beau-seidon/Promicroboy/other resources/build photos/back.jpg

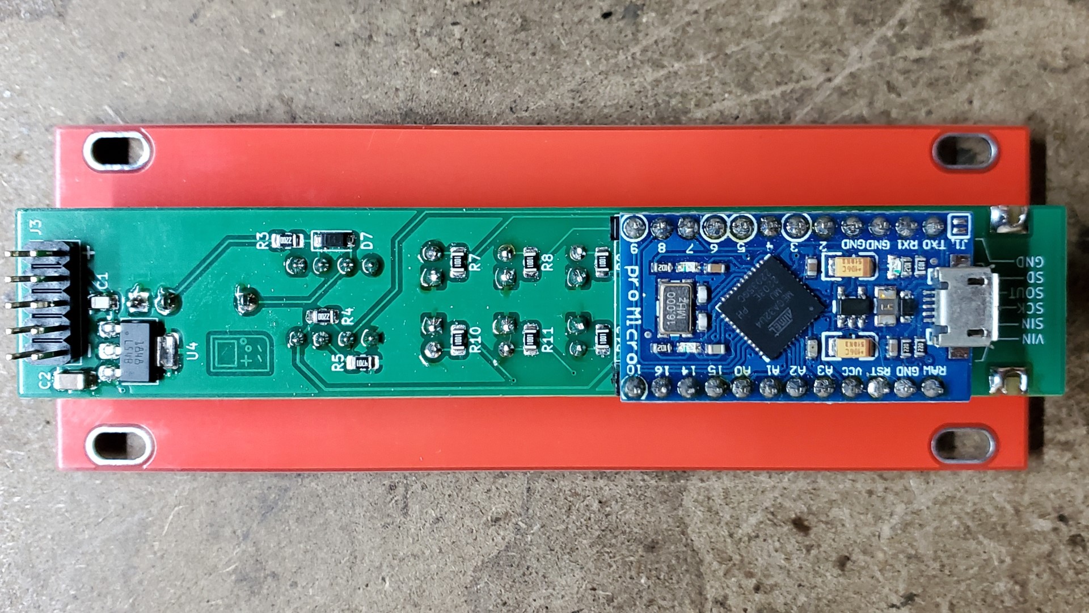
other resources/build photos/back.jpg
