beau-seidon/Promicroboy/other resources/build photos/link2.jpg

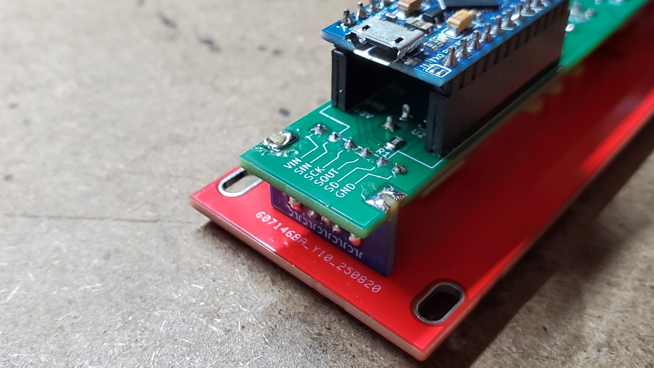
other resources/build photos/link2.jpg
