beau-seidon/Promicroboy/hardware/ProMicro16MHzv2.pdf

## Name

## Power

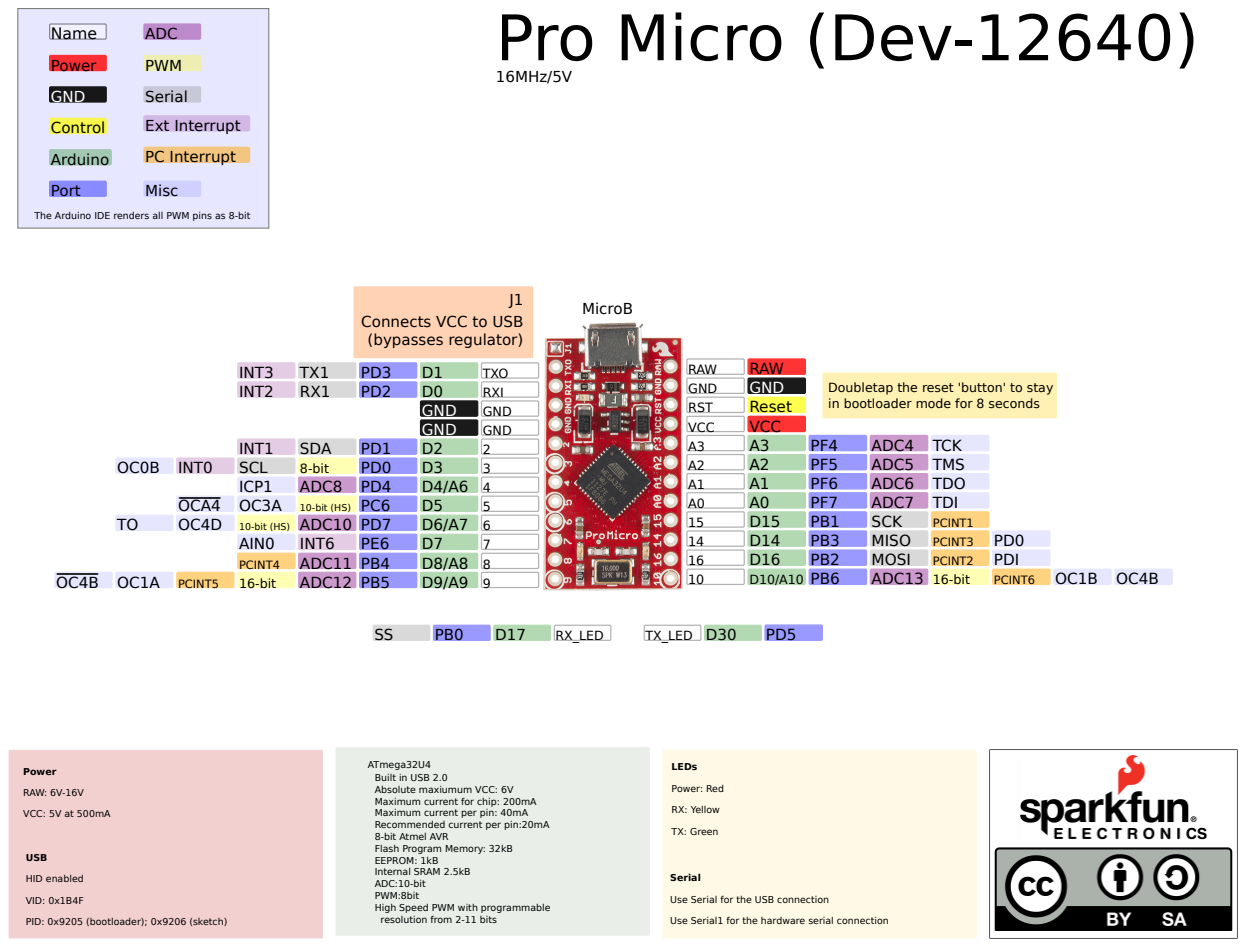
[picture p7: page 1]

The Arduino IDE renders all PWM pins as 8-bit

Connects VCC to USB
(bypasses regulator)

Doubletap the reset 'button' to stay
in bootloader mode for 8 seconds

ATmega32U4
Built in USB 2.0
Absolute maxiumum VCC: 6V
Maximum current for chip: 200mA
Maximum current per pin: 40mA
Recommended current per pin:20mA
8-bit Atmel AVR
Flash Program Memory: 32kB
EEPROM: 1kB
Internal SRAM 2.5kB
ADC:10-bit
PWM:8bit
High Speed PWM with programmable
resolution from 2-11 bits

Use Serial for the USB connection

Use Serial1 for the hardware serial connection
