beau-seidon/Promicroboy/software/src/Mode_LSDJ_Map.cpp

/**************************************************************************
 *  Name:   Timothy Lamb                                                  *
 *  Email:  trash80@gmail.com                                             *
 **************************************************************************/
/**************************************************************************
 *                                                                        *
 *  This program is free software; you can redistribute it and/or modify  *
 *  it under the terms of the GNU General Public License as published by  *
 *  the Free Software Foundation; either version 2 of the License, or     *
 *  (at your option) any later version.                                   *
 *                                                                        *
 **************************************************************************/

#include "Mode_LSDJ_Map.h"

#include "Led_Functions.h"
#include "Mode_MidiGb.h"
#include "Mode_Programmer.h"
#include "Mode.h"
#include "UsbMidi.h"


void modeLSDJMapSetup(void);
void modeLSDJMap(void);
void setMapByte(uint8_t b, boolean usb);
void setMapQueueMessage(uint8_t m, uint8_t wait);
void resetMapCue(void);
void checkMapQueue(void);
void usbMidiLSDJMapRealtimeMessage(uint8_t message);
void modeLSDJMapUsbMidiReceive(void);


void modeLSDJMapSetup()
{
    digitalWrite(pinStatusLed, LOW);
    pinMode(pinGBClock, OUTPUT);
    digitalWrite(pinGBClock, HIGH);

    blinkMaxCount = 1000;
    #ifdef USE_TEENSY
        usbMIDI.setHandleRealTimeSystem(usbMidiLSDJMapRealtimeMessage);
    #endif

    modeLSDJMap();
}


void modeLSDJMap()
{
    while (1) {
        setMode();    // check if the mode button was depressed

        modeLSDJMapUsbMidiReceive();
        checkMapQueue();

        if (serial->available()) {                // if MIDI Byte Availaibleleleiel
            incomingMidiByte = serial->read();    // read it

            checkForProgrammerSysex(incomingMidiByte);

            if (incomingMidiByte & 0x80) {     // if we have received a MIDI Status Byte
                switch (incomingMidiByte) {    // update cases with midi.h enum -b_s
                    case 0xF8:
                        setMapByte(0xFF, false);
                        usbMidiSendRTMessage(incomingMidiByte);
                        break;
                    case 0xFA:                                     // case: Transport Start Message
                    case 0xFB:                                     // and case: Transport Continue Message
                        sequencerStart();                          // start the sequencer
                        usbMidiSendRTMessage(incomingMidiByte);
                        break;
                    case 0xFC:                                     // case: Transport Stop Message
                        sequencerStop();
                        setMapByte(0xFE, false);
                        usbMidiSendRTMessage(incomingMidiByte);
                        break;
                    default:
                        midiData[0] = incomingMidiByte;
                        midiNoteOnMode = true;
                        if (midiData[0] == (0x90 + memory[MEM_LIVEMAP_CH])
                        || midiData[0] == (0x90 + (memory[MEM_LIVEMAP_CH] + 1))) resetMapCue();
                }

            } else if (midiNoteOnMode) {    // if we've received a message thats not a status and our note capture mode is true
                midiNoteOnMode = false;
                midiData[1] = incomingMidiByte;

                usbMidiSendTwoByteMessage(midiData[0], midiData[1]);
                if (midiData[0] == (0x90 + memory[MEM_LIVEMAP_CH])
                || midiData[0] == (0x90 + (memory[MEM_LIVEMAP_CH] + 1))) resetMapCue();

            } else {
                midiNoteOnMode = true;
                if (midiData[0] == (0x90 + memory[MEM_LIVEMAP_CH])
                || midiData[0] == (0x90 + (memory[MEM_LIVEMAP_CH] + 1))) {
                    if (incomingMidiByte) {
                        if (midiData[0] == (0x90 + (memory[MEM_LIVEMAP_CH] + 1))) {
                            setMapByte(128 + midiData[1], false);
                        } else {
                            setMapByte(midiData[1], false);
                        }
                    } else {
                        setMapByte(0xFE, false);
                    }
                } else if (midiData[0] == (0x80 + memory[MEM_LIVEMAP_CH])
                || midiData[0] == (0x80 + (memory[MEM_LIVEMAP_CH] + 1))) {
                    setMapByte(0xFE, false);
                }
                usbMidiSendThreeByteMessage(midiData[0], midiData[1], incomingMidiByte);
                checkMapQueue();
            }

        } else {
            updateStatusLight();
            checkMapQueue();
            updateBlinkLights();
        }
    }
}


void setMapByte(uint8_t b, boolean usb)
{
    uint8_t wait = mapQueueWaitSerial;
    if (usb) {
        wait = mapQueueWaitUsb;
    }

    switch (b) {
        case 0xFF:
            setMapQueueMessage(0xFF, wait);
            break;
        case 0xFE:
            if (!sequencerStarted) {
                sendByteToGameboy(0xFE);
            } else if (mapCurrentRow >= 0) {
                setMapQueueMessage(mapCurrentRow, wait);
            }
            break;
        default:
            mapCurrentRow = b;
            sendByteToGameboy(b);
            resetMapCue();
    }
}


void setMapQueueMessage(uint8_t m, uint8_t wait)
{
    if (mapQueueMessage == -1 || mapQueueMessage == 0xFF) {
        mapQueueTime = millis() + wait;
        mapQueueMessage = m;
    }
}


void resetMapCue()
{
    mapQueueMessage = -1;
}


void checkMapQueue()
{
    if (mapQueueMessage >= 0 && millis() > mapQueueTime) {
        if (mapQueueMessage == 0xFF) {
            sendByteToGameboy(mapQueueMessage);
        } else {
            if (mapQueueMessage == 0xFE || mapCurrentRow == mapQueueMessage) {
                // only kill playback if the row is the last one that's been played.
                mapCurrentRow = -1;
                sendByteToGameboy(0xFE);
            }
        }
        mapQueueMessage = -1;
        updateVisualSync();
    }
}


void usbMidiLSDJMapRealtimeMessage(uint8_t message)
{
    switch (message) {    // update cases with midi.h enum -b_s
        case 0xF8:
            setMapByte(0xFF, true);
        break;
        case 0xFA:               // case: Transport Start Message
        case 0xFB:               // and case: Transport Continue Message
            resetMapCue();
            sequencerStart();    // start the sequencer
        break;
        case 0xFC:               // case: Transport Stop Message
            sequencerStop();     // stop the sequencer
            setMapByte(0xFE, true);
        break;
    }
}


void modeLSDJMapUsbMidiReceive()
{
    #ifdef USE_TEENSY

        while (usbMIDI.read()) {
            uint8_t ch = usbMIDI.getChannel() - 1;
            if (ch != memory[MEM_LIVEMAP_CH] && ch != (memory[MEM_LIVEMAP_CH] + 1)) {
                continue;
            }
            switch (usbMIDI.getType()) {    // update cases with midi.h enum -b_s
                case 0x80:    // note off
                    setMapByte(0xFE, true);
                break;
                case 0x90:    // note on
                    if (ch == (memory[MEM_LIVEMAP_CH] + 1)) {
                        setMapByte(128 + usbMIDI.getData1(), true);
                    } else {
                        setMapByte(usbMIDI.getData1(), true);
                    }
                break;
                /*
                case 3:    // CC
                    break;
                case 4:    // PG
                    break;
                case 5:    // AT
                    break;
                case 6:    // PB
                    break;
                */
            }
        }
    #endif

    #ifdef USE_LEONARDO
        midiEventPacket_t rx;
        do {
            rx = MidiUSB.read();
            usbMidiLSDJMapRealtimeMessage(rx.byte1);
            uint8_t ch = rx.byte1 & 0x0F;
            if (ch != memory[MEM_LIVEMAP_CH] && ch != (memory[MEM_LIVEMAP_CH] + 1)) continue;
            switch (rx.header) {    // update cases with midi.h enum -b_s
                case 0x08:    // note off
                    setMapByte(0xFE, true);
                    break;
                case 0x09:    // note on
                    if (ch == (memory[MEM_LIVEMAP_CH] + 1))
                        setMapByte(128 + rx.byte2, true);
                    else
                        setMapByte(rx.byte2, true);
                    break;
            }
        } while (rx.header != 0);
    #endif
}
