beau-seidon/Promicroboy/software/src/Mode_LSDJ_Midiout.cpp

/**************************************************************************
 *  Name:   Timothy Lamb                                                  *
 *  Email:  trash80@gmail.com                                             *
 **************************************************************************/
/**************************************************************************
 *                                                                        *
 *  This program is free software; you can redistribute it and/or modify  *
 *  it under the terms of the GNU General Public License as published by  *
 *  the Free Software Foundation; either version 2 of the License, or     *
 *  (at your option) any later version.                                   *
 *                                                                        *
 **************************************************************************/

#include "Mode_LSDJ_Midiout.h"

#include "Led_Functions.h"
#include "MIDI_Out.h"
#include "Mode_Programmer.h"
#include "Mode.h"


void modeLSDJMidioutSetup(void);
void modeLSDJMidiout(void);
void midioutDoAction(byte m, byte v);
void checkStopNote(byte m);
void stopNote(byte m);
void playNote(byte m, byte n);
void playCC(byte m, byte n);
void playPC(byte m, byte n);
void stopAllNotes(void);
boolean getIncommingSlaveByte(void);


void modeLSDJMidioutSetup()
{
    digitalWrite(pinStatusLed, LOW);
    pinMode(pinGBClock, OUTPUT);
    digitalWrite(pinGBClock, HIGH);

    blinkMaxCount = 60;
    countGbClockTicks = 0;
    lastMidiData[0] = -1;
    lastMidiData[1] = -1;
    midiValueMode = false;

    modeLSDJMidiout();
}


void modeLSDJMidiout()
{
    while (1) {
        setMode();    // check if the mode button was depressed

        if (getIncommingSlaveByte()) {
            if (incomingMidiByte > 0x6f) {
                switch (incomingMidiByte) {    // update cases to midi.h enum -b_s
                    case 0x7F:    // clock tick
                        MIDI_sendRealTime(midi::Clock);
                        break;
                    case 0x7E:    // seq stop
                        MIDI_sendRealTime(midi::Stop);
                        stopAllNotes();
                        break;
                    case 0x7D:    // seq start
                        MIDI_sendRealTime(midi::Start);
                        break;
                    default:
                        midiData[0] = (incomingMidiByte - 0x70);
                        midiValueMode = true;
                        break;
                }
            } else if (midiValueMode == true) {
                midiValueMode = false;
                midioutDoAction(midiData[0], incomingMidiByte);
            }
        } else {
            updateBlinkLights();
            sMIDI.read();    // read from MIDI to detect programmer messages
            #ifdef HAS_USB_MIDI
                while (uMIDI.read());
            #endif
        }
    }
}


void midioutDoAction(byte m, byte v)
{
    if (m < 4) {
        // note message
        if (v) {
            checkStopNote(m);
            playNote(m, v);
        } else if (midiOutLastNote[m] >= 0) {
            stopNote(m);
        }
    } else if (m < 8) {
        m -= 4;
        // cc message
        playCC(m, v);
    } else if (m < 0x0C) {
        m -= 8;
        playPC(m, v);
    }
    blinkLight(0x90 + m, v);
}


void checkStopNote(byte m)
{
    if ((midioutNoteTimer[m] + midioutNoteTimerThreshold) < millis()) {
        stopNote(m);
    }
}


void stopNote(byte m)
{
    for (int x = 0; x < midioutNoteHoldCounter[m]; x++) {
        MIDI_sendNoteOff(midioutNoteHold[m][x], 0, memory[MEM_MIDIOUT_NOTE_CH + m] + 1);
    }
    midiOutLastNote[m] = -1;
    midioutNoteHoldCounter[m] = 0;
}


void playNote(byte m, byte n)
{
    MIDI_sendNoteOn(n, 127, memory[MEM_MIDIOUT_NOTE_CH + m] + 1);

    midioutNoteHold[m][midioutNoteHoldCounter[m]] = n;
    midioutNoteHoldCounter[m]++;
    midioutNoteTimer[m] = millis();
    midiOutLastNote[m] = n;
}


void playCC(byte m, byte n)
{
    byte v = n;

    if (memory[MEM_MIDIOUT_CC_MODE + m]) {
        if (memory[MEM_MIDIOUT_CC_SCALING + m]) {
            v = (v & 0x0F) * 8;
            // if (v) v--;
        }
        n = (m * 7) + ((n >> 4) & 0x07);
        MIDI_sendControlChange((memory[MEM_MIDIOUT_CC_NUMBERS + n]), v, memory[MEM_MIDIOUT_NOTE_CH + m] + 1);
    } else {
        if (memory[MEM_MIDIOUT_CC_SCALING + m]) {
            float s;
            s = n;
            v = ((s / 0x6f) * 0x7f);
        }
        n = (m * 7);
        MIDI_sendControlChange((memory[MEM_MIDIOUT_CC_NUMBERS + n]), v, memory[MEM_MIDIOUT_NOTE_CH + m] + 1);
    }
}


void playPC(byte m, byte n)
{
    MIDI_sendProgramChange(n, memory[MEM_MIDIOUT_NOTE_CH + m] + 1);
}


void stopAllNotes()
{
    for (int m = 0; m < 4; m++) {
        if (midiOutLastNote[m] >= 0) {
            stopNote(m);
        }
        MIDI_sendControlChange(123, 127, memory[MEM_MIDIOUT_NOTE_CH + m] + 1);
    }
}


boolean getIncommingSlaveByte()
{
    delayMicroseconds(midioutBitDelay);
    GB_SET(0, 0, 0);
    delayMicroseconds(midioutBitDelay);
    GB_SET(1, 0, 0);
    delayMicroseconds(2);
    if (digitalRead(pinGBSerialIn)) {
        incomingMidiByte = 0;
        for (countClockPause = 0; countClockPause != 7; countClockPause++) {
            GB_SET(0, 0, 0);
            delayMicroseconds(2);
            GB_SET(1, 0, 0);
            incomingMidiByte = (incomingMidiByte << 1) + digitalRead(pinGBSerialIn);
        }
        return true;
    }
    return false;
}
