beau-seidon/Promicroboy/software/src/Mode_Nanoloop.cpp

/**************************************************************************
 *  Name:   Timothy Lamb                                                  *
 *  Email:  trash80@gmail.com                                             *
 **************************************************************************/
/**************************************************************************
 *                                                                        *
 *  This program is free software; you can redistribute it and/or modify  *
 *  it under the terms of the GNU General Public License as published by  *
 *  the Free Software Foundation; either version 2 of the License, or     *
 *  (at your option) any later version.                                   *
 *                                                                        *
 **************************************************************************/

#include "Mode_Nanoloop.h"

#include "Led_Functions.h"
#include "Mode_Programmer.h"
#include "Mode.h"


void modeNanoloopSetup(void);
void modeNanoloopSync(void);
boolean sendTickToNanoloop(boolean state, boolean last_state);
void usbMidiNanoloopRealtimeMessage(uint8_t message);
void modeNanoloopUsbMidiReceive(void);


void modeNanoloopSetup()
{
    digitalWrite(pinStatusLed, LOW);
    pinMode(pinGBClock, OUTPUT);
    digitalWrite(pinGBClock, HIGH);

    blinkMaxCount = 1000;
    #ifdef USE_TEENSY
        usbMIDI.setHandleRealTimeSystem(usbMidiNanoloopRealtimeMessage);
    #endif

    modeNanoloopSync();
}


void modeNanoloopSync()
{
    while (1) {    // Loop forever
        setMode();    // check if the mode button was depressed

        modeNanoloopUsbMidiReceive();
        if (serial->available()) {                                                                          // if MIDI Byte Availaibleleleiel
            incomingMidiByte = serial->read();                                                              // read it
            if (!checkForProgrammerSysex(incomingMidiByte) && !usbMode) serial->write(incomingMidiByte);    // send it back to the Midi out

            if (incomingMidiByte & 0x80) {
                switch (incomingMidiByte) {
                    case midi::Clock:              // clock Message Recieved
                        if (sequencerStarted) {    // send a clock tick out if the sequencer is running
                            nanoSkipSync = !nanoSkipSync;
                            if (countSyncTime) {
                                nanoState = sendTickToNanoloop(nanoState, false);
                            } else {
                                nanoState = sendTickToNanoloop(true, true);
                            }
                            nanoState = sendTickToNanoloop(nanoState, nanoSkipSync);
                            updateVisualSync();
                            break;
                        }
                        break;
                    case midi::Start:       // Transport Start Message
                    case midi::Continue:    // Transport Continue Message
                        sequencerStart();
                        break;
                    case midi::Stop:        // Transport Stop Message
                        sequencerStop();
                        break;
                    default:
                        break;
                }
            }
        }

        updateStatusLight();
    }
}


boolean sendTickToNanoloop(boolean state, boolean last_state)
{
    if (!state) {
        if (last_state) {
            GB_SET(0, 1, 0);
            GB_SET(1, 1, 0);
        } else {
            GB_SET(0, 0, 0);
            GB_SET(1, 0, 0);
        }
        return true;
    } else {
        GB_SET(0, 1, 0);
        GB_SET(1, 1, 0);
        return false;
    }
}


void usbMidiNanoloopRealtimeMessage(uint8_t message)
{
    switch (message) {
        case midi::Clock:
            if (sequencerStarted) {
                nanoSkipSync = !nanoSkipSync;
                if (countSyncTime) {
                    nanoState = sendTickToNanoloop(nanoState, false);
                } else {
                    nanoState = sendTickToNanoloop(true, true);
                }
                nanoState = sendTickToNanoloop(nanoState, nanoSkipSync);
                updateVisualSync();
            }
            break;
        case midi::Start:        // case: Transport Start Message
        case midi::Continue:     // and case: Transport Continue Message
            sequencerStart();    // start the sequencer
            break;
        case midi::Stop:         // case: Transport Stop Message
            sequencerStop();
            break;
    }
}


void modeNanoloopUsbMidiReceive()
{
    #ifdef USE_TEENSY
        while (usbMIDI.read(memory[MEM_LSDJSLAVE_MIDI_CH] + 1)) {
            switch (usbMIDI.getType()) {
                case 0x90:    // note on
                    getSlaveSyncEffect(usbMIDI.getData1());
                break;
                /*
                case 0:    // note on
                    break;
                case 3:    // CC
                    break;
                case 4:    // PG
                    break;
                case 5:    // AT
                    break;
                case 6:    // PB
                    break;
                */
            }
        }
    #endif

    #ifdef HAS_USB_MIDI
        midiEventPacket_t rx;
        do {
            rx = MidiUSB.read();
            usbMidiNanoloopRealtimeMessage(rx.byte1);
        } while (rx.header != 0);
    #endif
}
