beau-seidon/Promicroboy/software/include/UsbMidi.h

#pragma once

#include "Arduinoboy.h"

#include <MIDI.h>


void usbMidiSendTwoByteMessage(uint8_t b1, uint8_t b2);
void usbMidiSendThreeByteMessage(uint8_t b1, uint8_t b2, uint8_t b3);
void usbMidiSendRTMessage(uint8_t b);
